acwright/6502-KIM/Models/0702461201.step

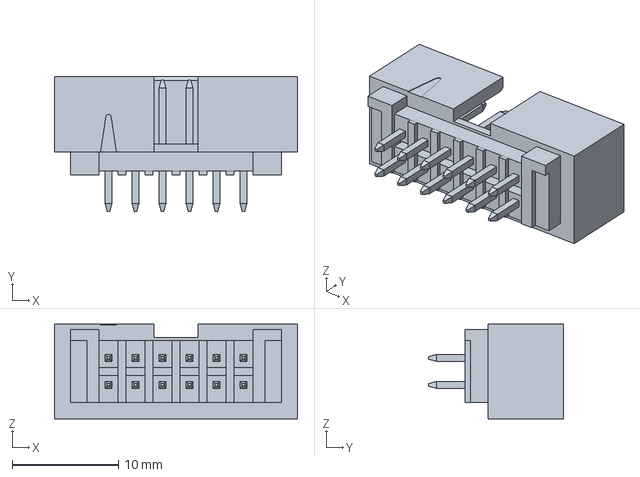
[picture p18: CAD file, 2026-05-05]
Models/0702461201.step
22.9 x 12.7 x 8.89 mm
