acwright/6502-KIM/Hardware/Keypad Expander/Rev 1.0/Keypad Expander.kicad_sch

## KiCad design Hardware/Keypad Expander/Rev 1.0/Keypad Expander.kicad_sch (2026-05-09)

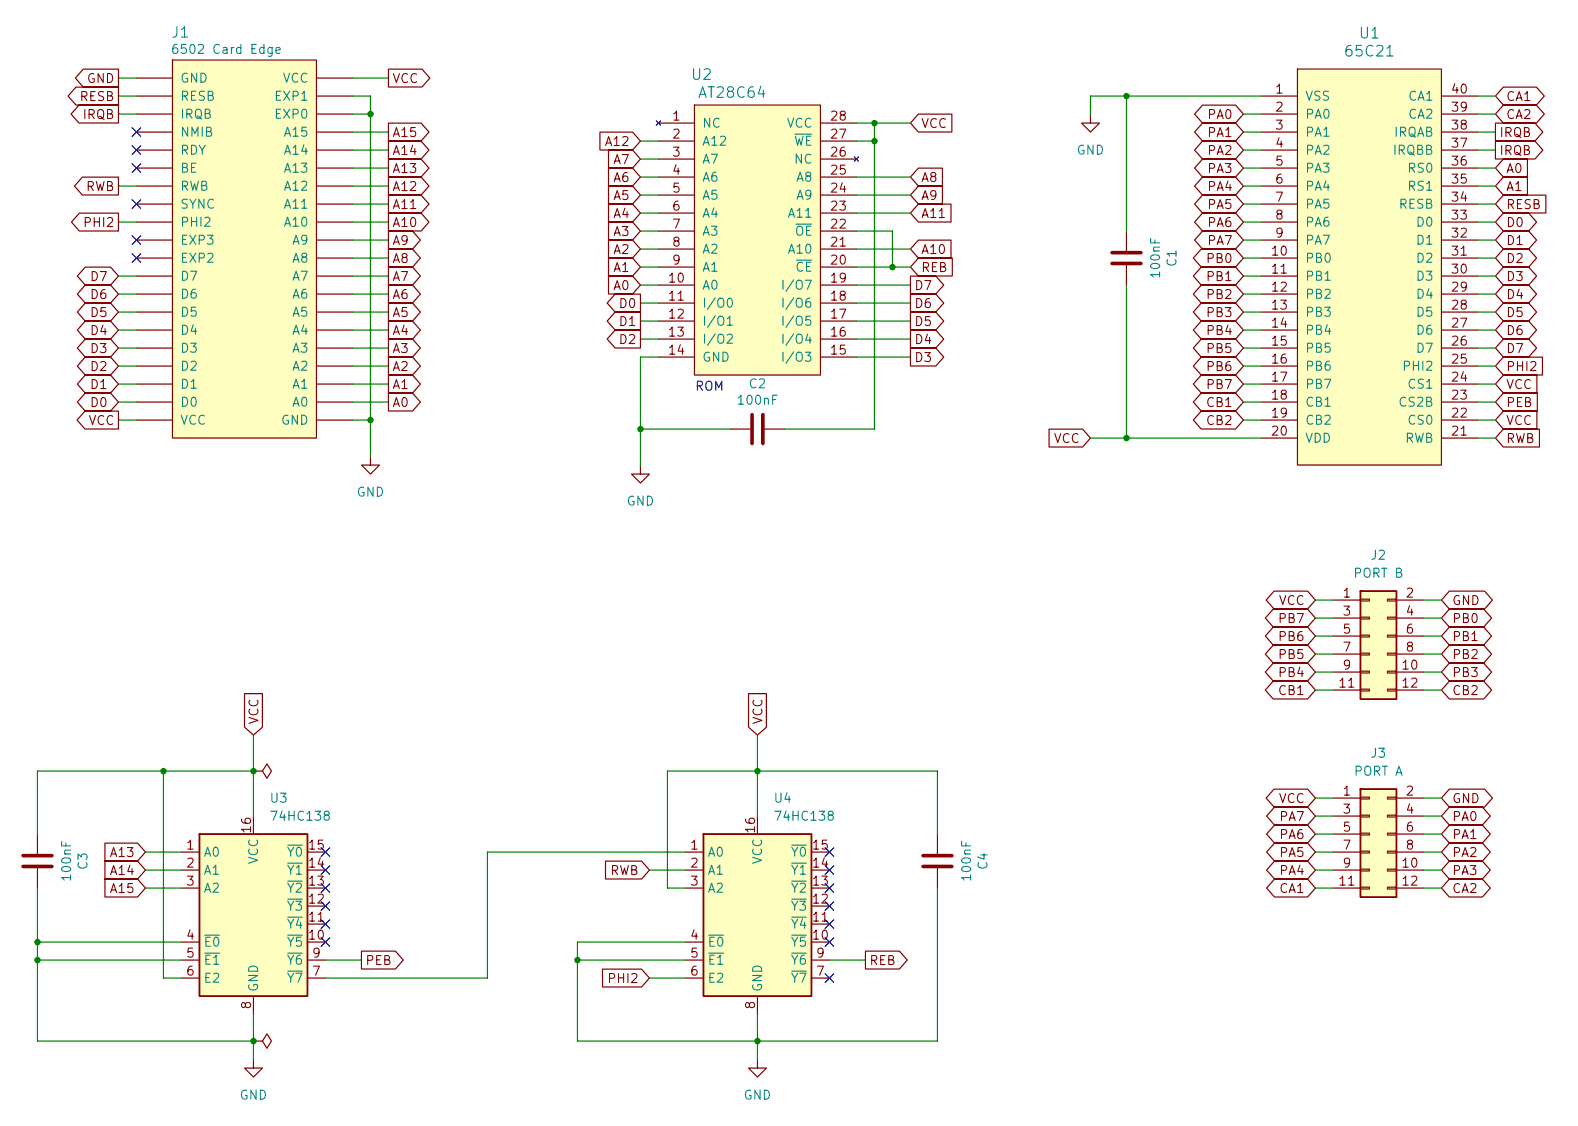
[picture p27: schematic Keypad Expander.kicad_sch]

Parts:
C1: 100nF; C_Disc_D5.0mm_W2.5mm_P5.00mm; LCSC C49678
C2, C3, C4: 100nF; C_Disc_D5.0mm_W2.5mm_P5.00mm
J1: 6502 Card Edge
J2: PORT B; 6502 GPIO Connector
J3: PORT A; 6502 GPIO Connector
U1: 65C21; DIP-40_W15.24mm_Socket_LongPads
U2: AT28C64; DIP-28_W15.24mm_Socket_LongPads
U3, U4: 74HC138; DIP-16_W7.62mm_Socket_LongPads

Connections:
A0: J1.A0, U1.36 (RS0), U2.10 (A0)
A1: J1.A1, U1.35 (RS1), U2.9 (A1)
A2: J1.A2, U2.8 (A2)
A3: J1.A3, U2.7 (A3)
A4: J1.A4, U2.6 (A4)
A5: J1.A5, U2.5 (A5)
A6: J1.A6, U2.4 (A6)
A7: J1.A7, U2.3 (A7)
A8: J1.A8, U2.25 (A8)
A9: J1.A9, U2.24 (A9)
A10: J1.A10, U2.21 (A10)
A11: J1.A11, U2.23 (A11)
A12: J1.A12, U2.2 (A12)
A13: J1.A13, U3.1 (A0)
A14: J1.A14, U3.2 (A1)
A15: J1.A15, U3.3 (A2)
CA1: J3.11, U1.40 (CA1)
CA2: J3.12, U1.39 (CA2)
CB1: J2.11, U1.18 (CB1)
CB2: J2.12, U1.19 (CB2)
D0: J1.D0, U1.33 (D0), U2.11 (I/O0)
D1: J1.D1, U1.32 (D1), U2.12 (I/O1)
D2: J1.D2, U1.31 (D2), U2.13 (I/O2)
D3: J1.D3, U1.30 (D3), U2.15 (I/O3)
D4: J1.D4, U1.29 (D4), U2.16 (I/O4)
D5: J1.D5, U1.28 (D5), U2.17 (I/O5)
D6: J1.D6, U1.27 (D6), U2.18 (I/O6)
D7: J1.D7, U1.26 (D7), U2.19 (I/O7)
GND: C1.1, C2.2, C3.2, C4.2, J1.EXP0, J1.EXP1, J1.GND, J2.2, J3.2, U1.1 (VSS), U2.14 (GND), U3.4 (~E0), U3.5 (~E1), U3.8 (GND), U4.4 (~E0), U4.5 (~E1), U4.8 (GND)
IRQB: J1.IRQB, U1.37 (IRQBB), U1.38 (IRQAB)
unnamed: U3.7 (~Y7), U4.1 (A0)
PA0: J3.4, U1.2 (PA0)
PA1: J3.6, U1.3 (PA1)
PA2: J3.8, U1.4 (PA2)
PA3: J3.10, U1.5 (PA3)
PA4: J3.9, U1.6 (PA4)
PA5: J3.7, U1.7 (PA5)
PA6: J3.5, U1.8 (PA6)
PA7: J3.3, U1.9 (PA7)
PB0: J2.4, U1.10 (PB0)
PB1: J2.6, U1.11 (PB1)
PB2: J2.8, U1.12 (PB2)
PB3: J2.10, U1.13 (PB3)
PB4: J2.9, U1.14 (PB4)
PB5: J2.7, U1.15 (PB5)
PB6: J2.5, U1.16 (PB6)
PB7: J2.3, U1.17 (PB7)
PEB: U1.23 (CS2B), U3.9 (~Y6)
PHI2: J1.PHI2, U1.25 (PHI2), U4.6 (E2)
REB: U2.20 (~CE), U2.22 (~OE), U4.9 (~Y6)
RESB: J1.RESB, U1.34 (RESB)
RWB: J1.RWB, U1.21 (RWB), U4.2 (A1)
VCC: C1.2, C2.1, C3.1, C4.1, J1.VCC, J2.1, J3.1, U1.20 (VDD), U1.22 (CS0), U1.24 (CS1), U2.27 (~WE), U2.28 (VCC), U3.6 (E2), U3.16 (VCC), U4.3 (A2), U4.16 (VCC)

Notes on the sheet:
ROM
